ecilasun/sandpiper_pcb/enclosure2/leftbody.SLDPRT

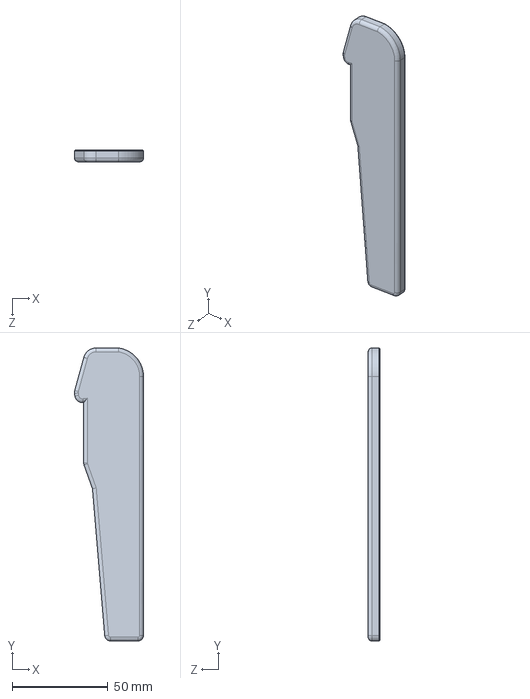
[picture p16: CAD file, 2025-08-07]
enclosure2/leftbody.SLDPRT
36.1 x 153.2 x 6.10 mm
