ecilasun/sandpiper_pcb/enclosure2/platemidtop.SLDPRT

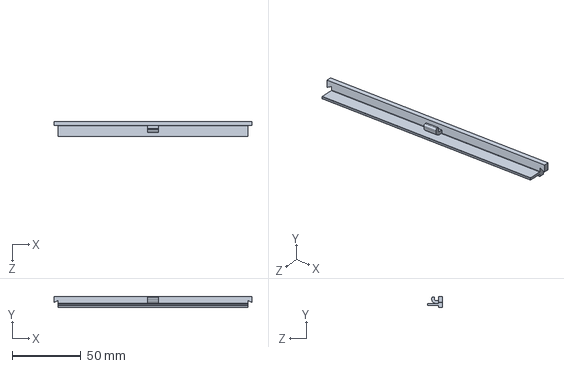
[picture p17: CAD file, 2025-08-07]
enclosure2/platemidtop.SLDPRT
144.5 x 8.00 x 11.1 mm
