ecilasun/sandpiper_pcb/keyboard/enclosure/enclosure.SLDASM

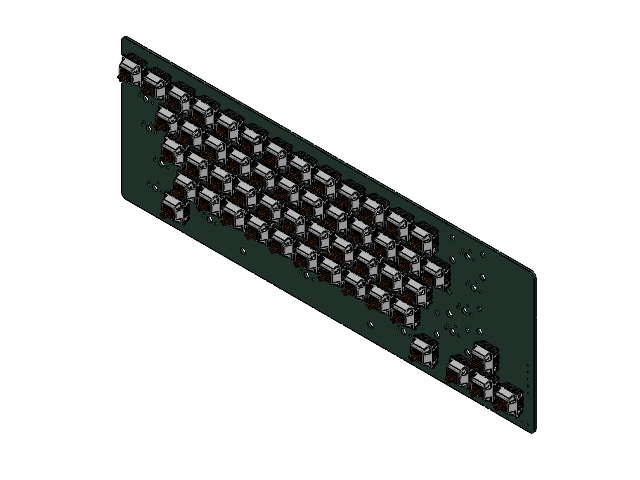
[picture p18: CAD file, 2025-05-29]
keyboard/enclosure/enclosure.SLDASM
SW_Cherry_MX_PCB_cp.step x 52
D_SOD_323.step x 63
keyboard_PCB.step
