ecilasun/sandpiper_pcb/enclosure/enclosure.SLDASM

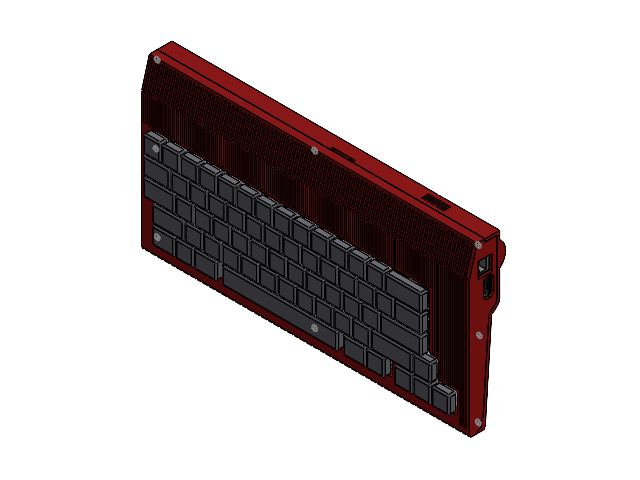
[picture p19: CAD file, 2025-12-06]
enclosure/enclosure.SLDASM
MX_PCB.step x 63
MX_1.00u_CAD.step x 52
Stabilizer_MX_2.00u.step x 3
MX_2.25u_CAD.step x 2
MX_1.75u_CAD.step x 2
MX_1.25u_CAD.step x 3
MX_2.00u_CAD.step
MX_1.50u_CAD.step x 2
Stabilizer_MX_6.25u.step
MX_6.25u_CAD.step
PinHeader_1x04_P2.54mm_Vertical.step
PinHeader_2x03_P2.54mm_Vertical.step
C_0805_2012Metric.step x 8
D_SOD-323.step x 63
R_0805_2012Metric.step x 4
TQFP-44_10x10mm_P0.8mm.step
LED_1206_3216Metric.step
Crystal_SMD_3225-4Pin_3.2x2.5mm.step
USB_C_Receptacle_GCT_USB4085.step
SW_Tactile_SPST_NO_Straight_CK_PTS636Sx25SMTRLFS.step
keyboard_PCB.step
USB_C_Receptacle_GCT_USB4105-xx-A_16P_TopMnt_Horizontal.step x 2
BGA-484_23.0x23.0mm_Layout22x22_P1.0mm.step
HDMI_A_Molex_208658-1001_Horizontal.step
PinHeader_2x20_P2.54mm_Vertical.step x 2
USB_A_TE_292303-7_Horizontal.step
RJ45_Molex_9346520x_Horizontal.step
smartzynqmock_PCB.step
profile
faceplate
